herculanodavi/guitar-pedal/pcb/simulation/sallen_key_3rd_order_butterworth.asc

C1: cap; 1n
C2: cap; 1n
R1: res; 6k8
R2: res; 22k
R3: res; 12k
U1: opamp
V1: voltage; ""; AC 1
Named nets: 0, Vin
.ac dec 100 1 50k
.lib opamp.sub
