herculanodavi/guitar-pedal/pcb/simulation/adc_frontend_first_stage.asc

C1: cap; 150p
C2: cap; 100n
R1: res; 1k
R2: res; 2200k
R3: res; 2200k
V1: voltage; 1.65
V2: voltage; ""; AC 1
Named nets: 0, Vcom, Signal, Vout
.ac dec 100 1 2Meg
