herculanodavi/guitar-pedal/pcb/simulation/single-ended_to_differential.asc

C3: cap; 150p
R4: res; 1k
R5: res; 1k
V1: voltage; ""; AC 1
Named nets: 0, Vminus, Vplus
.ac dec 100 1 1Meg
